PiniponSelvagem/Cybertruck-RC/photos/01_day_side_front__halfsize.jpg

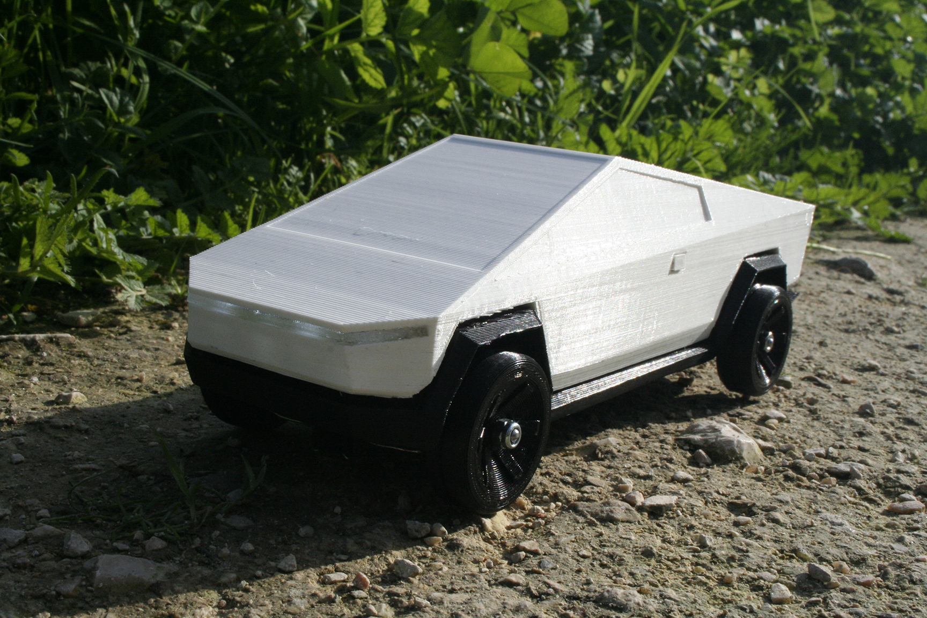
photos/01_day_side_front__halfsize.jpg
