PiniponSelvagem/Cybertruck-RC/photos/03_day_front__halfsize.jpg

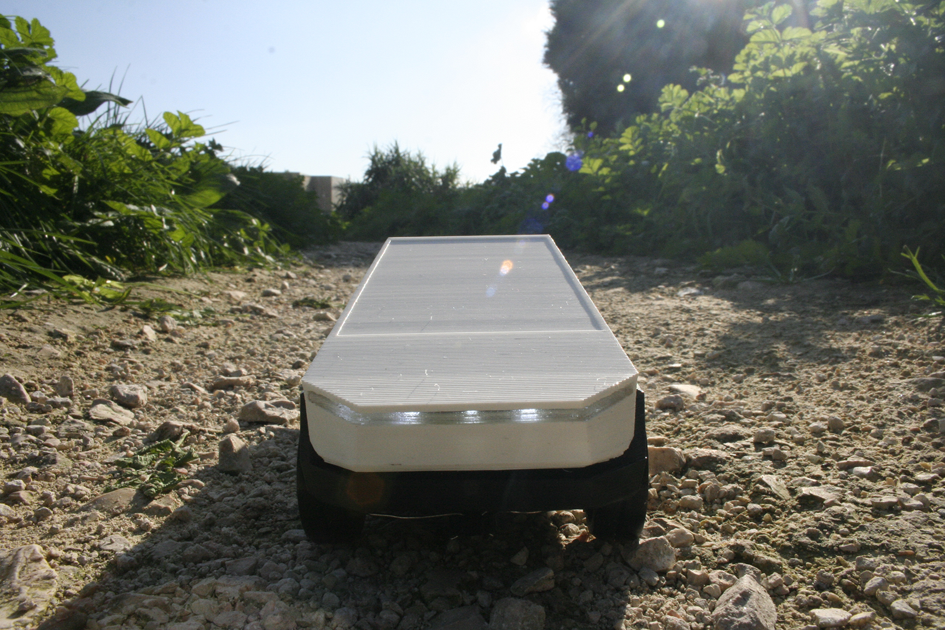
photos/03_day_front__halfsize.jpg
