PiniponSelvagem/Cybertruck-RC/photos/05_day_topdown__halfsize.jpg

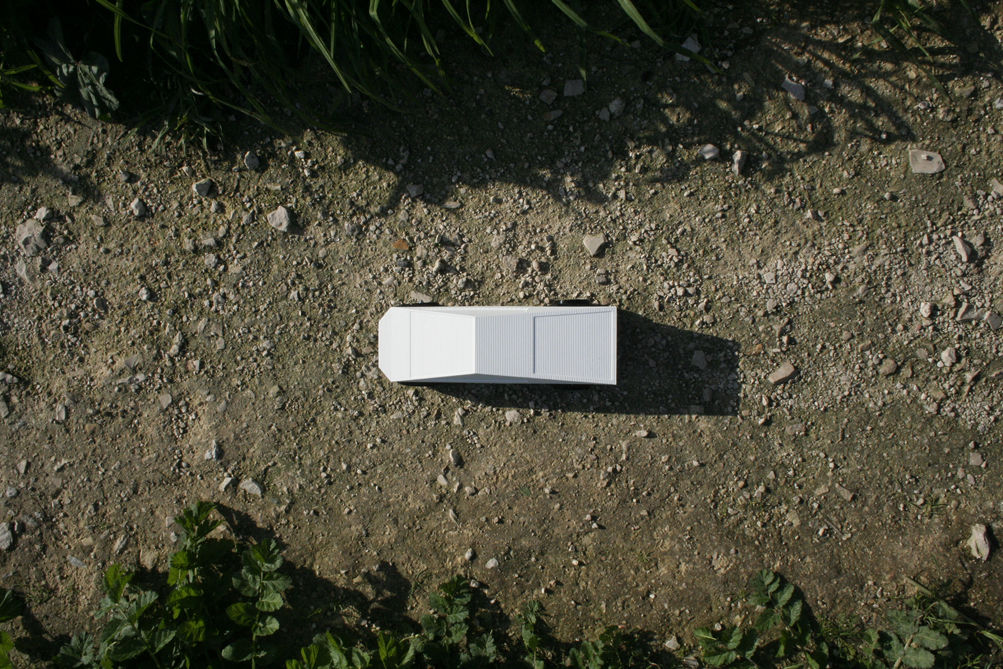
photos/05_day_topdown__halfsize.jpg
