PiniponSelvagem/Cybertruck-RC/photos/07_day_bottom_back__halfsize.jpg

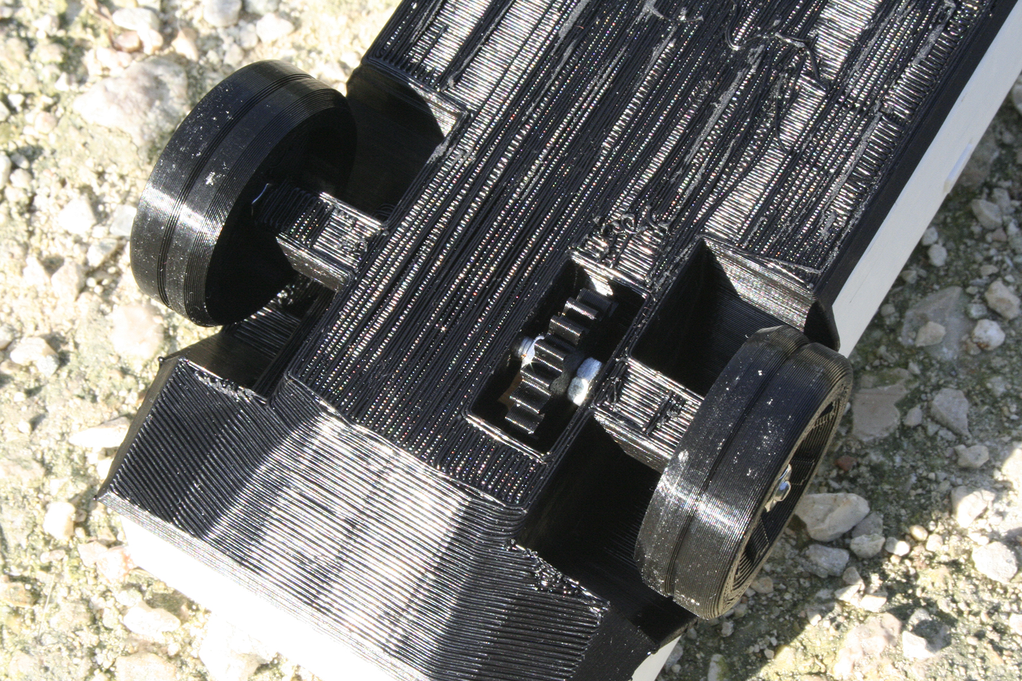
photos/07_day_bottom_back__halfsize.jpg
