PiniponSelvagem/Cybertruck-RC/photos/08_day_bottom_front__halfsize.jpg

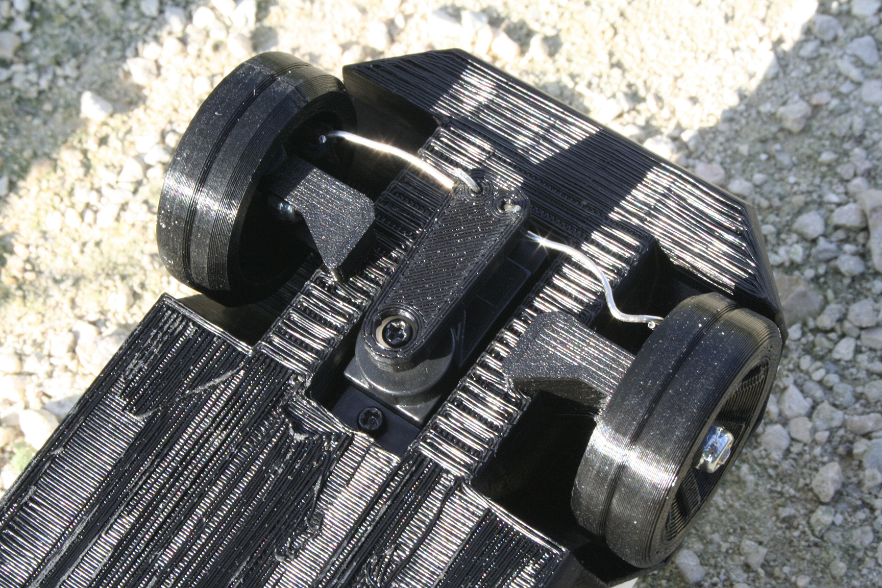
photos/08_day_bottom_front__halfsize.jpg
