PiniponSelvagem/Cybertruck-RC/photos/09_night_side_front__halfsize.jpg

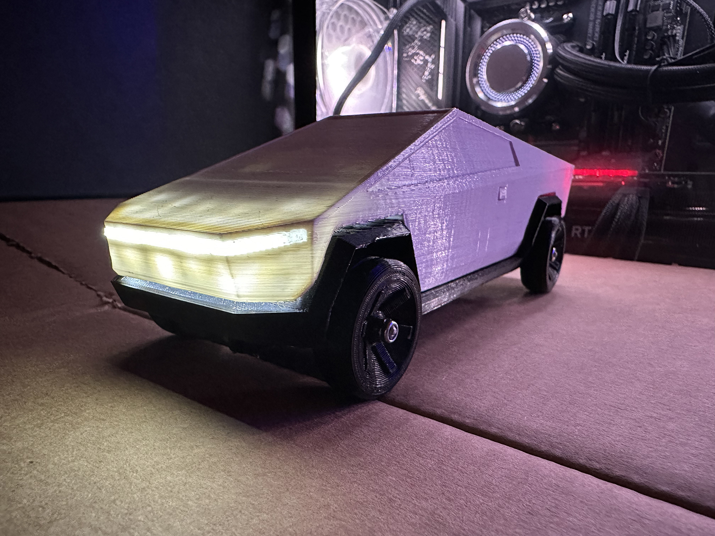
photos/09_night_side_front__halfsize.jpg
