PiniponSelvagem/Cybertruck-RC/photos/11_night_front__halfsize.jpg

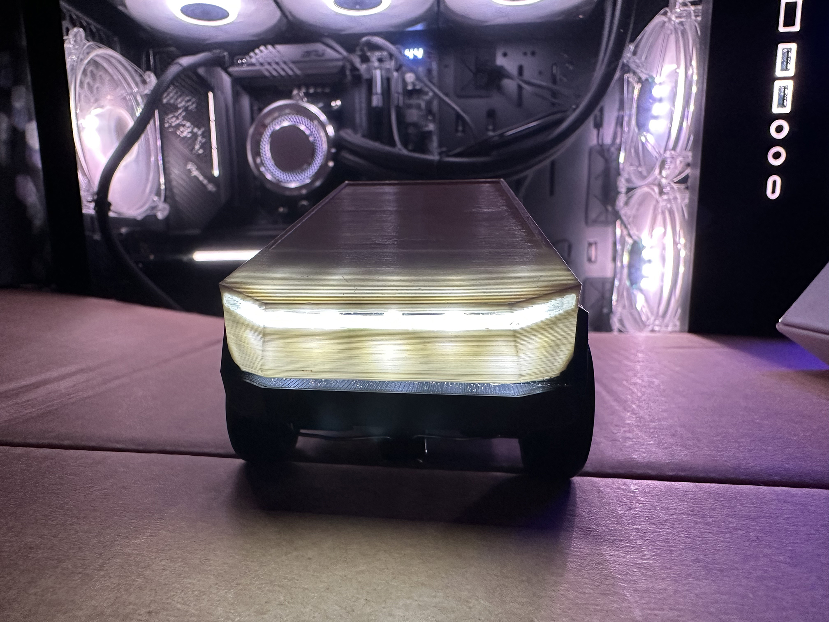
photos/11_night_front__halfsize.jpg
