PiniponSelvagem/Cybertruck-RC/photos/12_night_back__halfsize.jpg

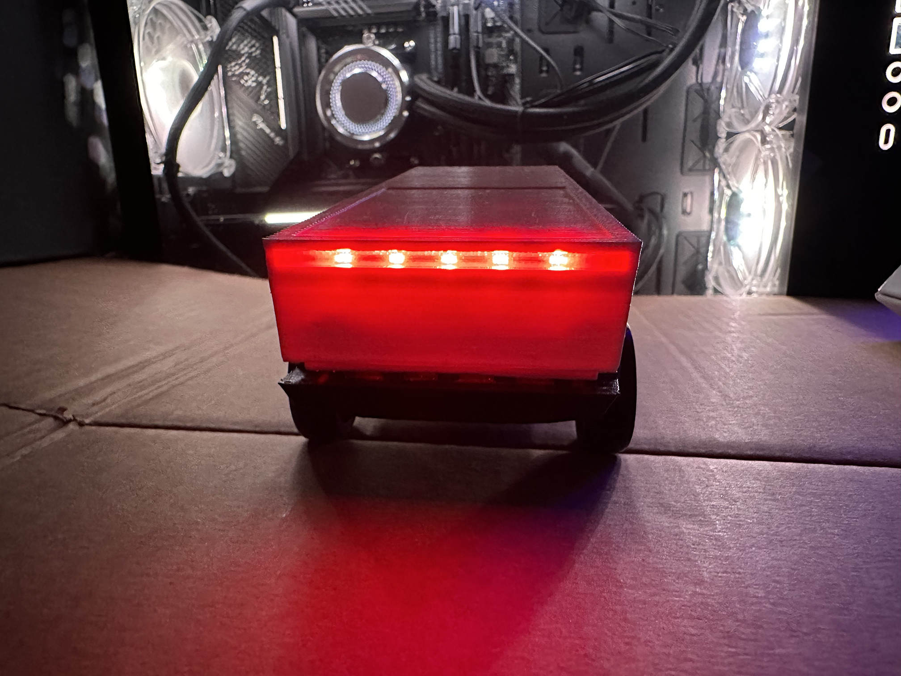
photos/12_night_back__halfsize.jpg
