PiniponSelvagem/Cybertruck-RC/photos/13_night_wheel_front__halfsize.jpg

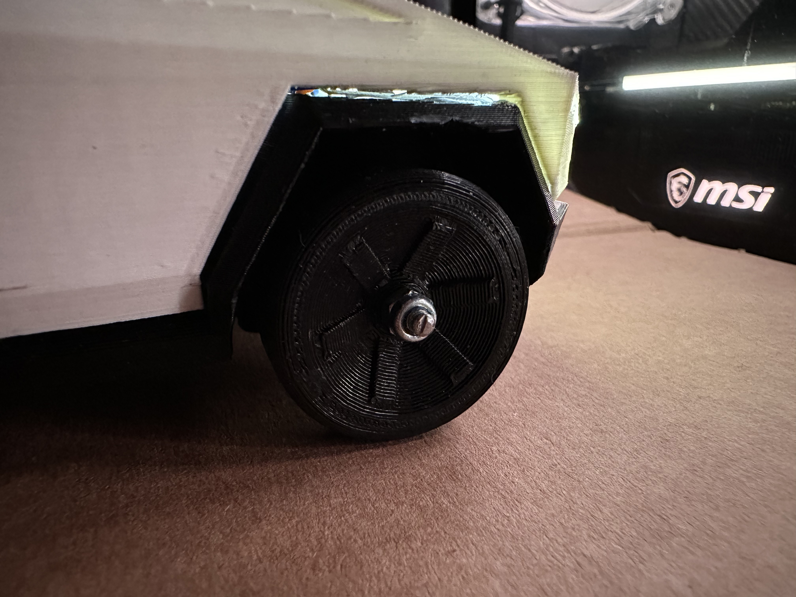
photos/13_night_wheel_front__halfsize.jpg
