PiniponSelvagem/Cybertruck-RC/photos/14_night_wheel_back__halfsize.jpg

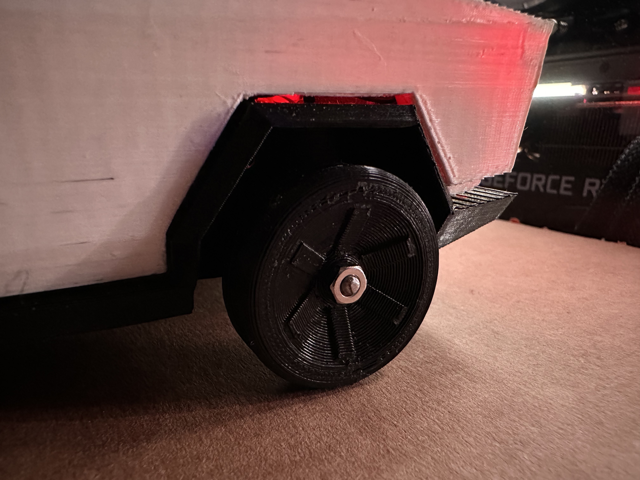
photos/14_night_wheel_back__halfsize.jpg
