PiniponSelvagem/Cybertruck-RC/photos/16_inside_lights-off__halfsize.jpg

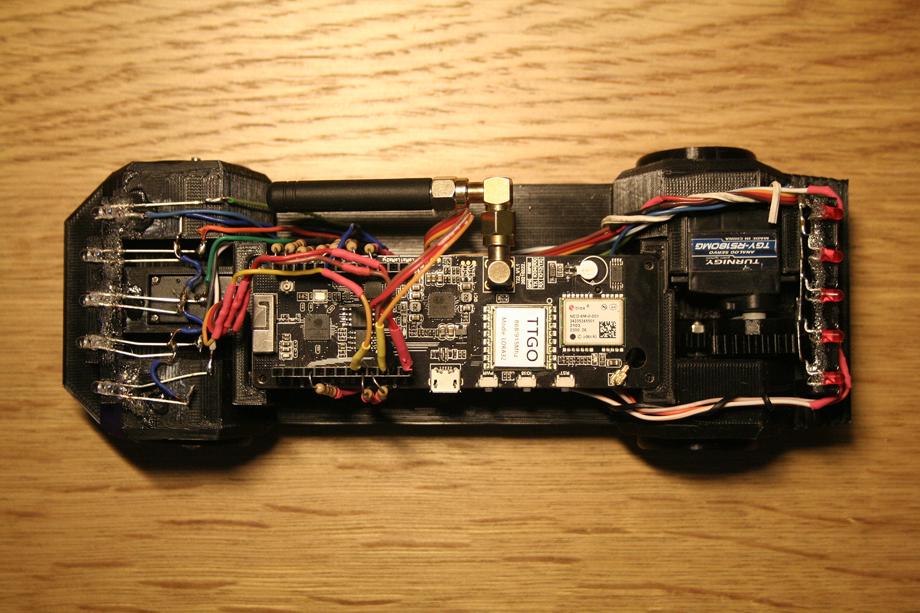
photos/16_inside_lights-off__halfsize.jpg
