PiniponSelvagem/Cybertruck-RC/photos/17_inside_lights-on__halfsize.jpg

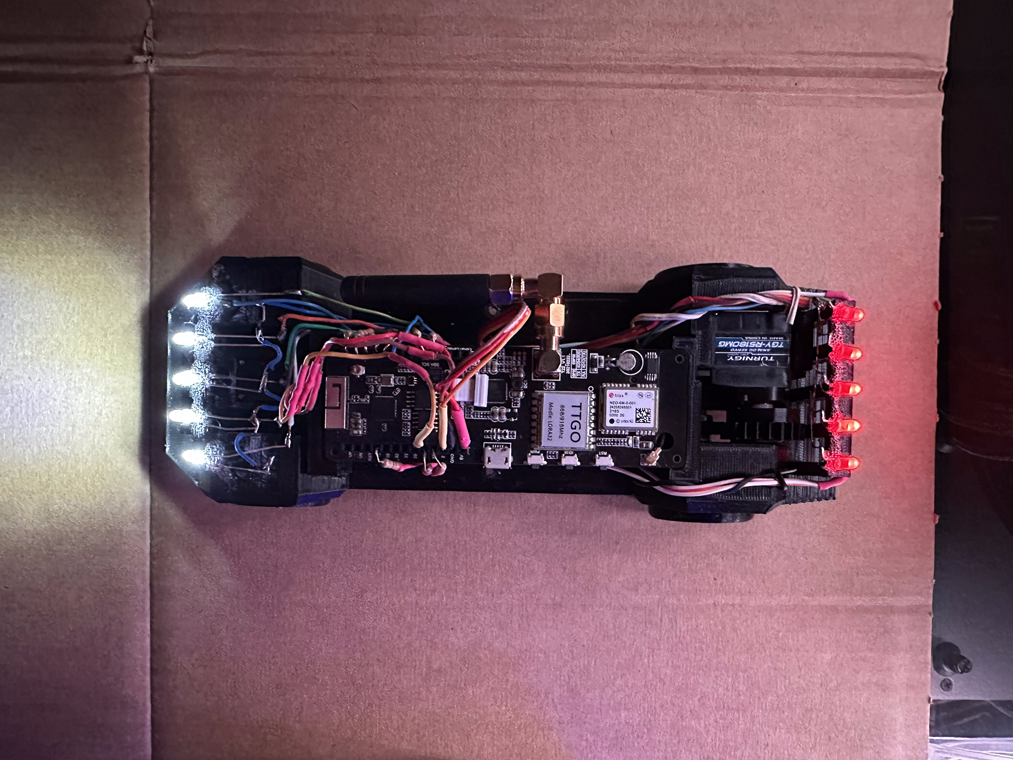
photos/17_inside_lights-on__halfsize.jpg
