PiniponSelvagem/Cybertruck-RC/photos/18_inside_front_lights_on__halfsize.jpg

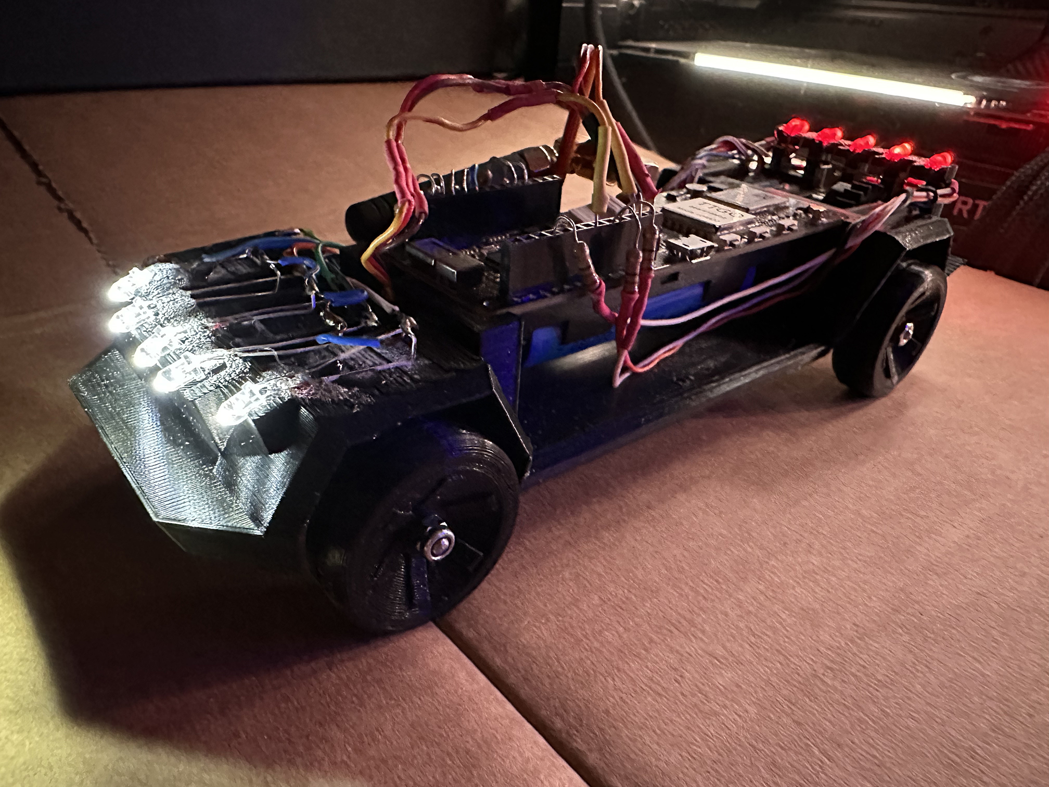
photos/18_inside_front_lights_on__halfsize.jpg
