PiniponSelvagem/Cybertruck-RC/photos/YT_demo_picture_below-2mb.jpg

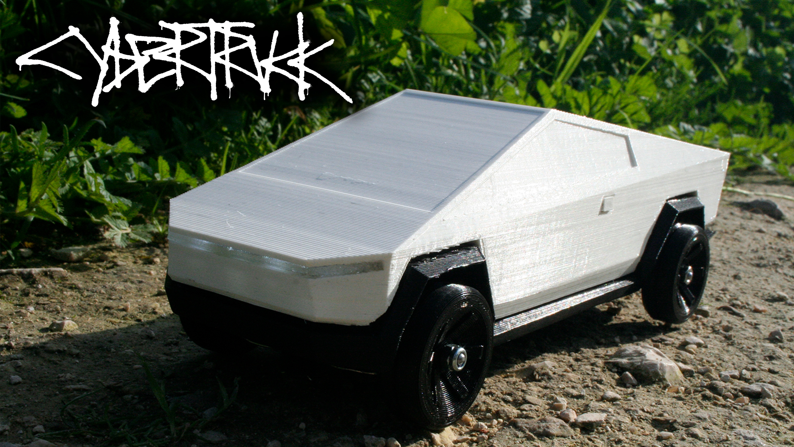
photos/YT_demo_picture_below-2mb.jpg
